bwack/C64C-250469-KiCAD-Replica/images/250469.gif

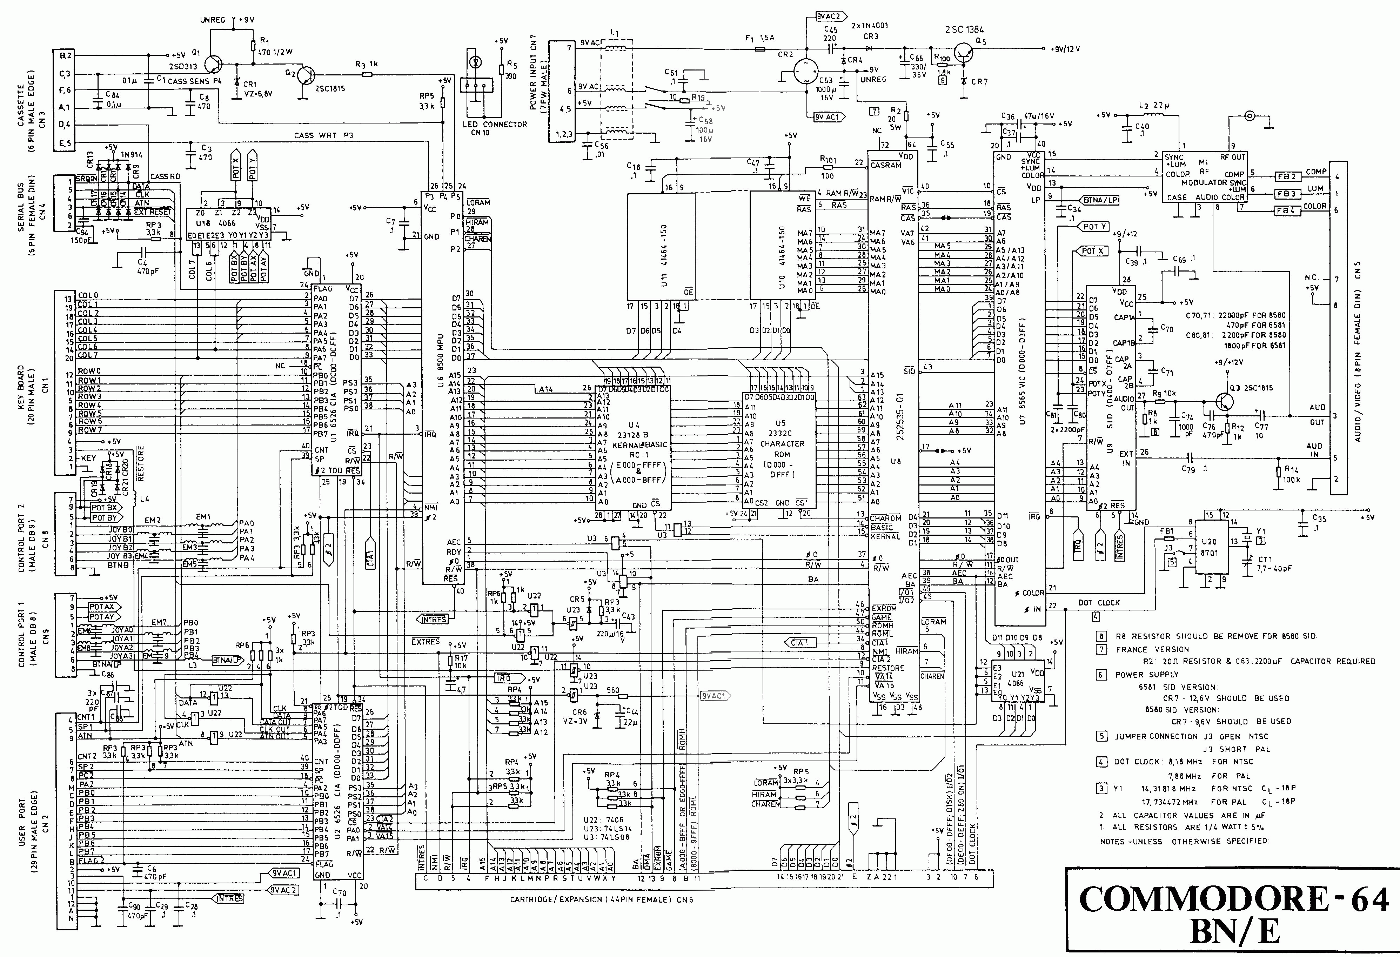
images/250469.gif
