bwack/C64C-250469-KiCAD-Replica/images/252312.jpg

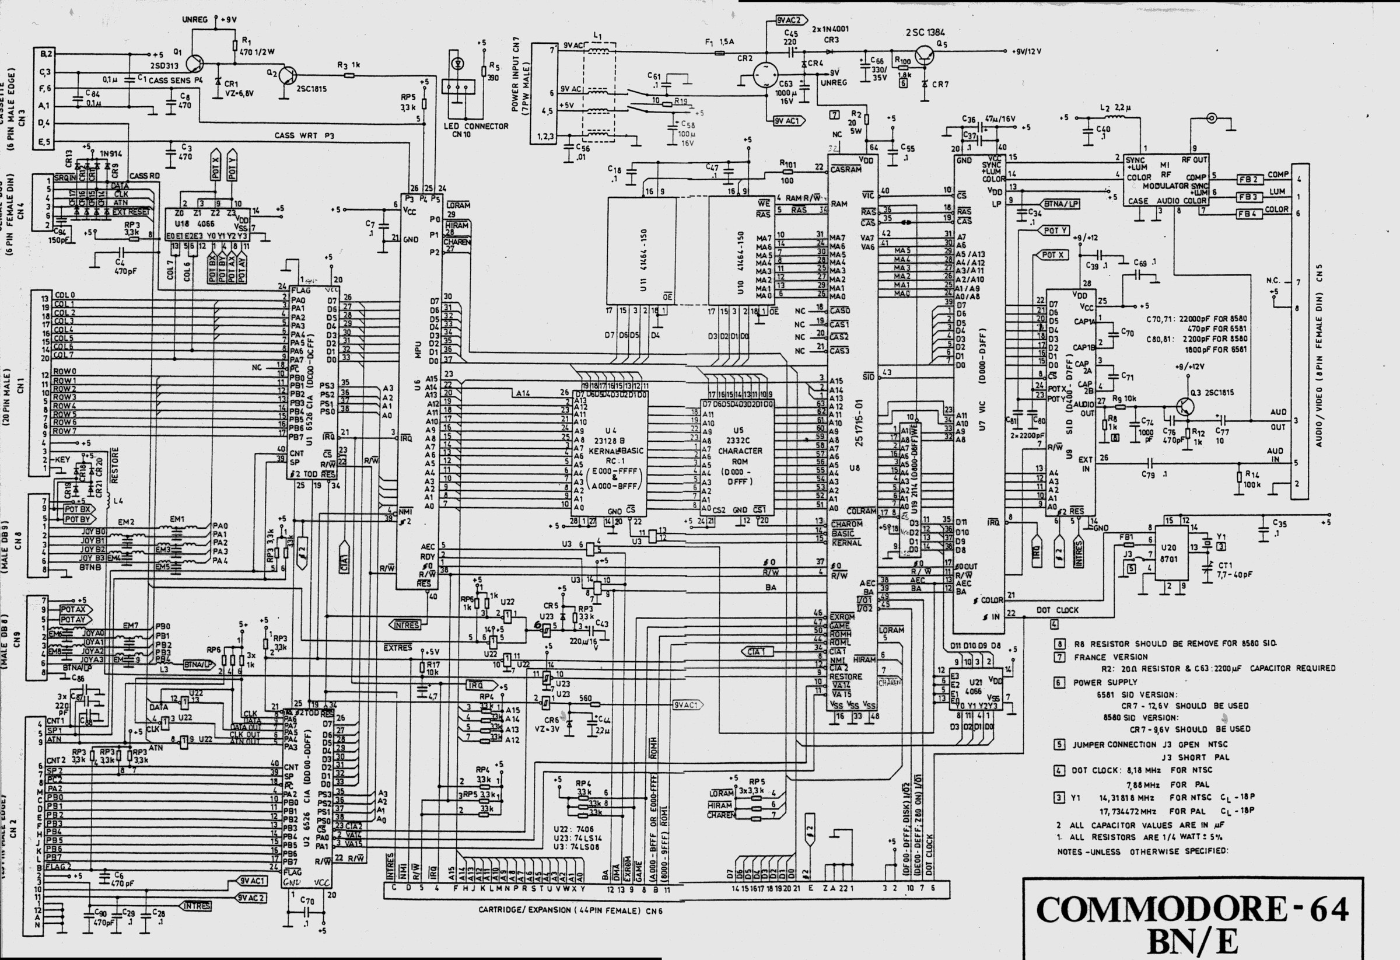
images/252312.jpg
