bwack/C64C-250469-KiCAD-Replica/C64-250469-KiCad.kicad_sch

## KiCad design C64-250469-KiCad.kicad_sch (2023-05-16)

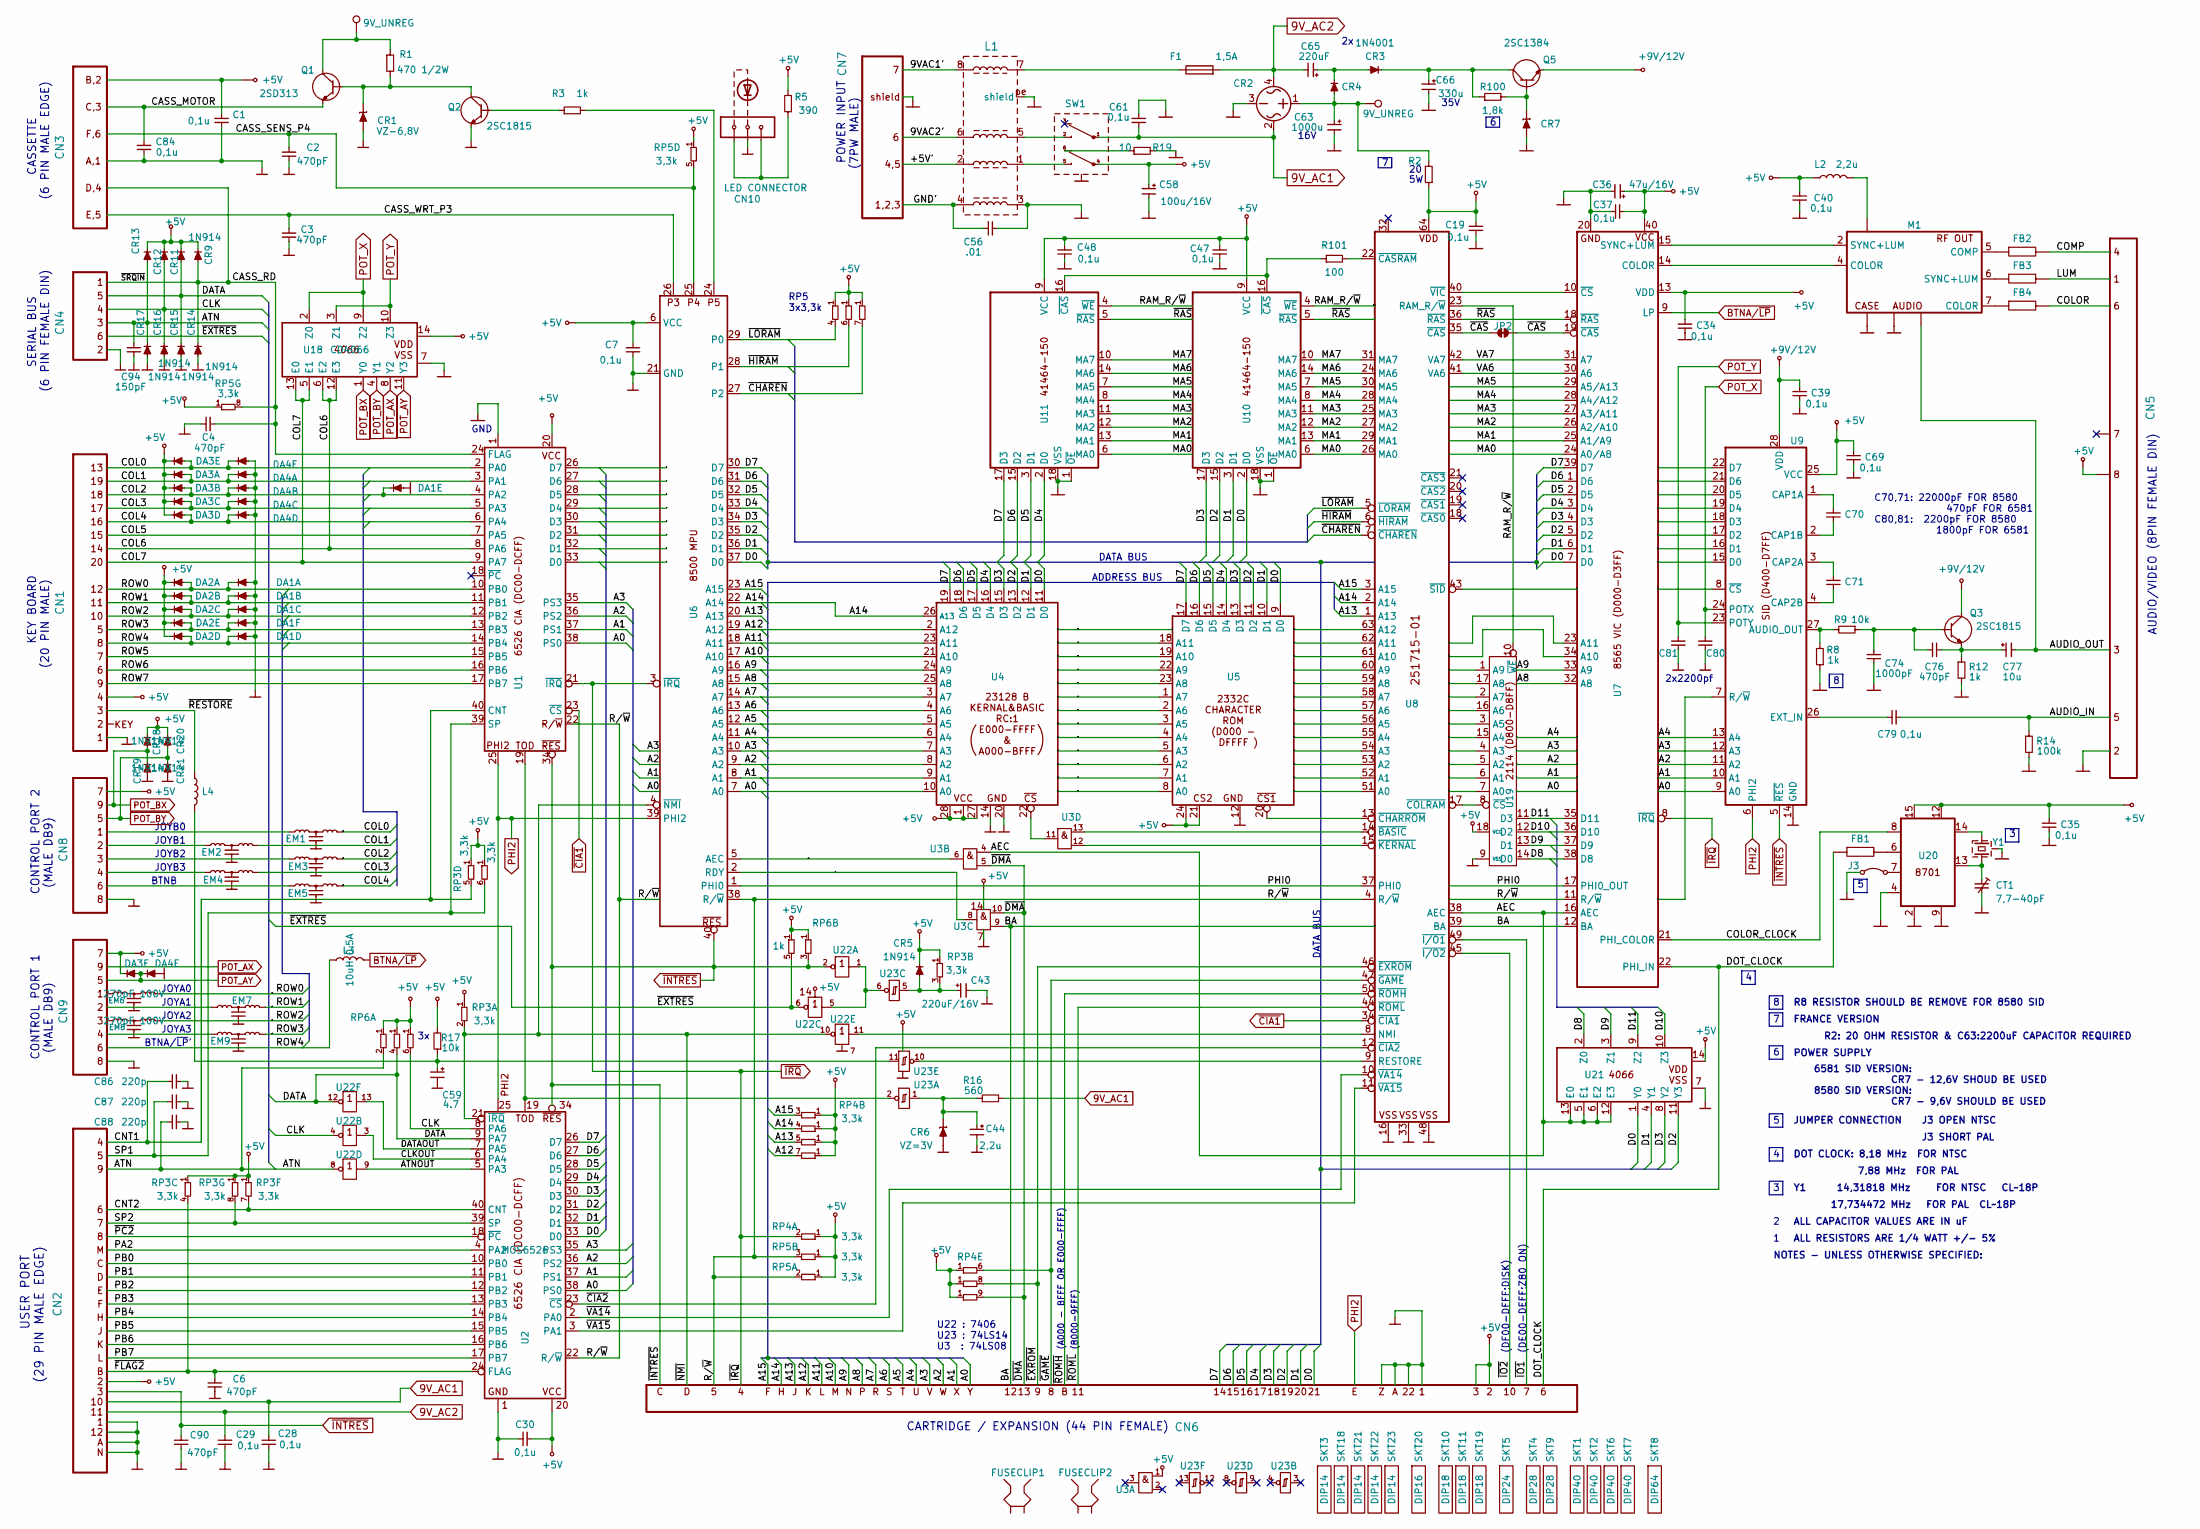
[picture p8: schematic C64-250469-KiCad.kicad_sch]

Parts:
C1, C7, C19, C28, C29, C30, C34, C35, C37, C39, C40, C47, C48, C61, C69, C79, C84: 0,1u; CAP_DISC_P100mil; Mouser 81-RCER71H104K0K1H3B
C2, C3, C4, C6, C76, C90: 470pF; CAP_DISC_P100mil; Mouser 81-RCER71H471K0M1H3A
C36: 47u/16V; CAP_RADIAL_P5.08MM_D6MM; Mouser 667-ECA-1CM470B
C43: 220uF/16V; CAP_RADIAL_P5.08MM_D6MM; Mouser 667-ECA-1CHG221B
C44: 2,2u; CAP_RADIAL_P5.08MM_D6MM; Mouser 667-ECA-1HHG2R2B
C56: .01; CAP_DISC_P100mil; Mouser 81-RCER71H103K0M1H3A
C58: 100u/16V; CAP_RADIAL_P5.12MM_D10MM; Mouser 667-ECA-1CHG101B
C59: 4.7; CAP_RADIAL_P5.08MM_D6MM; Mouser 667-ECE-A1EKS4R7B
C63: 1000u; CAP_AXIAL_BIG; Mouser 594-MAL212535102E3
C65: 220uF; CAP_RADIAL_P5.12MM_D12MM; Mouser 667-EEU-EB1E221SB
C66: 330u; CAP_RADIAL_P5.12MM_D12MM; Mouser 667-ECA-1VM471B
C70, C71: SeeTable; CAP_DISC_P100mil; Mouser 81-RCER71H223K0K1H3B
C74: 1000pF; CAP_DISC_P100mil; Mouser 81-RCER71H102K0M1H3A
C77: 10u; CAP_RADIAL_P5.08MM_D6MM; Mouser 667-ECA-1EM100B
C80, C81: 2200pF; CAP_DISC_P100mil; Mouser 81-RCER71H222K0M1H3A
C86, C87, C88: 220p; CAP_DISC_P100mil; Mouser 81-RCER71H221K0M1H3A
C94: 150pF; CAP_DISC_P100mil; Mouser 81-RCE5C1H151J0K1H3B
CN1: KEYBOARD_CONN_20pinlist; Mouser 855-M20-9992045
CN2: EDGE_CON_24P_USERPORT
CN3: EDGE_CON_12P_TAPE
CN4: SERIAL_CON_DIN6
CN5: AV_CON_DIN8
CN6: EXPANSION_PORT
CN7: POWER_CON_D7_250407
CN8, CN9: JOYPORT_DB9; Digi-Key 625-009-262-033-ND
CN10: LED CONNECTOR; LED; Mouser 855-M20-9992045
CR1: VZ-6,8V; RECTIFIER; Mouser 78-1N5235B
CR2: BRIDGE_RECTIFIER; Mouser 583-BR34
CR3, CR4: 1N4001; RECTIFIER; Mouser 625-1N4001-E3/54
CR5, CR9, CR11, CR12, CR13, CR14, CR15, CR16, CR17, CR18, CR19, CR20, CR21: 1N914; RECTIFIER; Mouser 78-1N4148
CR6: VZ=3V; RECTIFIER; Mouser 78-1N5225B-TAP
CR7: See [6] in schema; RECTIFIER; Mouser 78-1N5240B
CT1: 7,7-40pF; CAP_VARIABLE; Digi-Key 2447-GKG30015-ND
DA1, DA4: DIODE_ARRAY_COMMON_Anoda; diodepackage; Mouser NU
DA2, DA3: DIODE_ARRAY_COMMON_CATHODE; diodepackage; Mouser NU
EM1, EM2, EM3, EM4, EM5, EM6, EM7, EM8, EM9: 270pF 100V; T-FILTER; Mouser 81-DSS1NB32A271Q91A
F1: 1,5A; FUSE; Mouser 504-BK/AGC-1-1/2-R
FB1: FERRITE_BEAD_TWO_TURN; FERRITE_P200mil_STANDING; Mouser 81-BL02RN2R1M2B
FB2, FB3, FB4: FERRITE_BEAD; FERRITE_P200mil_STANDING; Mouser 81-BL01RN1A1F1J
FUSECLIP1, FUSECLIP2: Mouser 504-BK/1A1907-06-R
J3: JUMPER_NO
JP2: SolderJumper_Closed; JUMPER_CLOSED
L1: CHOKE; CHOKE_FILTER; Digi-Key ?
L2: 2,2u; INDUCTOR_P500mil; Mouser 652-78F2R2J-RC
L3, L4: 10uH 0.5A; INDUCTOR_P200mil; Mouser 80-SBT-0210
M1: Modulator
Q1: 2SD313; TO-220-3_Horizontal_TabDown_250407; Digi-Key TIP29AGOS-ND
Q2, Q3: 2SC1815; Q_NPN_ECB; Digi-Key 1514-2SC1815PBFREE-ND
Q5: 2SC1384; Q_NPN_ECB; Digi-Key KSD1616AGTATB-ND
R1: 470 1/2W; RESISTOR_AXIAL_600MIL; Digi-Key 13-MFR50SFRF52-470RCT-ND
R2: SeeTable; POWER_RESISTOR; Digi-Key Not Used
R3, R8, R12: 1k; RESISTOR_P200mil_STANDING; Digi-Key 13-MFR-25FTF52-1KCT-ND
R5: 390; RESISTOR_P200mil_STANDING; Digi-Key MFR-25FBF52-390R-ND
R9, R17: 10k; RESISTOR_P200mil_STANDING; Digi-Key 13-MFR-25FRF52-10KCT-ND
R14: 100k; RESISTOR_P200mil_STANDING; Digi-Key 13-MFR-25FRF52-100KCT-ND
R16: 560; RESISTOR_P200mil_STANDING; Digi-Key MFR-25FBF52-560R-ND
R19: 10; RESISTOR_AXIAL_600MIL; Digi-Key 13-MFR50SFTE52-10RCT-ND
R100: 1,8k; RESISTOR_P200mil_STANDING; Digi-Key 13-MFR-25FTE52-1K8CT-ND
R101: 100; RESISTOR_P200mil_STANDING; Digi-Key 100XBK-ND
RP3, RP5: 3,3k; RP_ARRAY_7WAY; Digi-Key 4608X-1-332LF-ND
RP4: 3,3k; RP_ARRAY_8WAY; Digi-Key 4609X-101-332LF-ND
RP6: 1k; RP_ARRAY_5WAY; Digi-Key 4606X-1-102LF-ND
SKT1, SKT2, SKT6, SKT7: DIP40; Digi-Key 1175-1481-ND
SKT3, SKT18, SKT21, SKT22, SKT23: DIP14; Digi-Key 1175-1476-ND
SKT4, SKT9: DIP28; Digi-Key 1175-1480-ND
SKT5: DIP24; Digi-Key 1175-2554-ND
SKT8: DIP64; Digi-Key D8864-42-ND
SKT10, SKT11, SKT19: DIP18; Digi-Key 1175-1478-ND
SKT20: DIP16; Digi-Key 1175-1477-ND
SW1: POWER_SWITCH; Digi-Key 360-4016-ND
U1, U2: MOS6526; PDIP-40
U3: 74LS08; PDIP-14; Mouser 595-SN74HCT08N
U4: 27128B; PDIP-28
U5: 2332C; PDIP-24
U6: 8500; PDIP-40
U7: VIC_II; PDIP-40
U8: 251715-01; PLA_252535-01
U9: SID; PDIP-28
U10, U11: 4164 DRAM; PDIP-18
U18, U21: CD4066; PDIP-14; Digi-Key 296-2061-5-ND
U19: COLOR_RAM_2114; PDIP-18
U20: MOS8701; PDIP-16
U22: 74LS06; PDIP-14; Mouser 595-SN7406NE4
U23: 74LS14; PDIP-14; Mouser 595-SN74HCT14N
Y1: 17.734475 MHz; CRYSTAL; Digi-Key 887-2042-ND

Connections:
9VAC1': CN7.7, L1.8
9VAC2': CN7.6, L1.6
9V_AC1: C28.1, C61.2, CN2.10, CR2.2, R16.2, SW1.1
9V_AC2: C29.1, C65.2, CN2.11, CR2.4, F1.2
9V_UNREG: C63.1, CR2.1, CR4.2 (A), Q1.C, R1.1, R2.2
+5V: C1.1, C7.1, C19.1, C30.2, C34.1, C35.1, C36.1, C37.2, C40.1, C47.1, C48.1, C58.1, C69.1, CN1.4, CN2.2, CN3.2, CN3.B, CN5.8 (VCC), CN6.2, CN6.3, CN8.7, CN9.7, CR5.1 (KATODE), CR9.1 (KATODE), CR11.1 (KATODE), CR12.1 (KATODE), CR13.1 (KATODE), CR18.1 (KATODE), CR20.1 (KATODE), DA2.4 (KATODE), DA3.4 (KATODE), L2.1, R2.1, R5.2, R17.2, RP3.1, RP4.1, RP5.1, RP6.1, SW1.4, U1.20 (VCC), U2.20 (VCC), U3.1, U3.14 (VDD), U4.1 (VCC), U4.27 (VCC), U4.28 (VCC), U5.21 (CS2), U5.24 (VCC), U6.6 (VCC), U7.13 (VDD), U7.40 (GND), U8.64 (VDD), U9.25 (VCC), U10.9 (VCC), U11.9 (VCC), U18.14 (VDD), U19.18 (VCC), U20.12, U20.15, U21.14 (VDD), U22.14, U23.14
+5V': CN7.4, CN7.5, L1.2
+9V/12V: C39.1, Q3.C, Q5.E, U9.28 (VDD)
A0: CN6.Y, U1.38 (PS0), U2.38 (PS0), U4.10 (A0), U5.8 (A0), U6.7 (A0), U8.51 (A0), U9.9 (A0), U19.7 (A0)
A1: CN6.X, U1.37 (PS1), U2.37 (PS1), U4.9 (A1), U5.7 (A1), U6.8 (A1), U8.52 (A1), U9.10 (A1), U19.6 (A1)
A2: CN6.W, U1.36 (PS2), U2.36 (PS2), U4.8 (A2), U5.6 (A2), U6.9 (A2), U8.53 (A2), U9.11 (A2), U19.5 (A2)
A3: CN6.V, U1.35 (PS3), U2.35 (PS3), U4.7 (A3), U5.5 (A3), U6.10 (A3), U8.54 (A3), U9.12 (A3), U19.4 (A3)
A4: CN6.U, U4.6 (A4), U5.4 (A4), U6.11 (A4), U8.55 (A4), U9.13 (A4), U19.15 (A4)
A5: CN6.T, U4.5 (A5), U5.3 (A5), U6.12 (A5), U8.56 (A5), U19.3 (A5)
A6: CN6.S, U4.4 (A6), U5.2 (A6), U6.13 (A6), U8.57 (A6), U19.16 (A6)
A7: CN6.R, U4.3 (A7), U5.1 (A7), U6.14 (A7), U8.58 (A7), U19.2 (A7)
A8: CN6.P, U4.25 (A8), U5.23 (A8), U6.15 (A8), U7.32 (A8), U8.59 (A8), U19.17 (A8)
A9: CN6.N, U4.24 (A9), U5.22 (A9), U6.16 (A9), U7.33 (A9), U8.60 (A9), U19.1 (A9)
A10: CN6.M, U4.21 (A10), U5.19 (A10), U6.17 (A10), U7.34 (A10), U8.61 (A10)
A11: CN6.L, U4.23 (A11), U5.18 (A11), U6.18 (A11), U7.23 (A11), U8.62 (A11)
A12: CN6.K, RP4.7, U4.2 (A12), U6.19 (A12), U8.63 (A12)
A13: CN6.J, RP4.5, U6.20 (A13), U8.1 (A13)
A14: CN6.H, RP4.4, U4.26 (A13), U6.22 (A14), U8.2 (A14)
A15: CN6.F, RP4.3, U6.23 (A15), U8.3 (A15)
AEC: U3.4, U7.16 (AEC), U8.38 (AEC), U21.5 (E1), U21.6 (E2), U21.12 (E3), U21.13 (E0)
AEC&~DMA: U3.6, U6.5 (AEC)
ATN: C88.2, C94.1, CN2.9, CN4.3, CR13.2 (A), CR17.1 (KATODE), RP6.2, U22.8
ATNOUT: U2.5 (PA3), U22.9
AUDIO_IN: C79.2, CN5.5 (AUDIO_IN), R14.1
AUDIO_OUT: C77.2, CN5.3 (AUDIO_OUT), M1.8 (AUDIO)
BA: CN6.12, U3.9, U7.12 (BA), U8.39 (BA)
BTNA/~LP: L3.2, U7.9 (LP)
CASS_MOTOR: C84.1, CN3.3, CN3.C, Q1.E
CASS_RD: C4.1, CN3.4, CN3.D, CN4.1, CR9.2 (A), CR14.1 (KATODE), RP5.8, U1.24 (FLAG)
CASS_SENS_P4: C2.1, CN3.6, CN3.F, RP5.5, U6.25 (P4)
CASS_WRT_P3: C3.1, CN3.5, CN3.E, U6.26 (P3)
CLK: CN4.4, CR12.2 (A), CR16.1 (KATODE), RP6.6, U2.8 (PA6), U22.4
CLKOUT: U2.6 (PA4), U22.3
CNT1: C86.2, CN2.4, RP3.5, U1.40 (CNT)
CNT2: CN2.6, RP3.7, U2.40 (CNT)
COL0: CN1.13, DA3.6 (A), DA4.7 (KATODE), EM1.3, U1.2 (PA0)
COL1: CN1.19, DA3.1 (A), DA4.1 (KATODE), EM2.3, U1.3 (PA1)
COL2: CN1.18, DA1.6 (KATODE), DA3.2 (A), DA4.2 (KATODE), EM3.3, U1.4 (PA2)
COL3: CN1.17, DA3.3 (A), DA4.3 (KATODE), EM4.3, U1.5 (PA3)
COL4: CN1.16, DA3.5 (A), DA4.5 (KATODE), EM5.3, U1.6 (PA4)
COL5: CN1.15, U1.7 (PA5)
COL6: CN1.14, U1.8 (PA6), U18.6 (E2), U18.12 (E3)
COL7: CN1.20, U1.9 (PA7), U18.5 (E1), U18.13 (E0)
COLOR: CN5.6 (COLOR), FB4.2
COLOR_CLOCK: U7.21 (PHI_COLOR), U20.8
COMP: CN5.4 (COMP), FB2.2
D0: CN6.21, U1.33 (D0), U2.33 (D0), U4.11 (D0), U5.9 (D0), U6.37 (D0), U7.7 (D0), U9.15 (D0), U10.2 (D0), U21.1 (Y0)
D1: CN6.20, U1.32 (D1), U2.32 (D1), U4.12 (D1), U5.10 (D1), U6.36 (D1), U7.6 (D1), U9.16 (D1), U10.3 (D1), U21.4 (Y1)
D2: CN6.19, U1.31 (D2), U2.31 (D2), U4.13 (D2), U5.11 (D2), U6.35 (D2), U7.5 (D2), U9.17 (D2), U10.15 (D2), U21.11 (Y3)
D3: CN6.18, U1.30 (D3), U2.30 (D3), U4.15 (D3), U5.13 (D3), U6.34 (D3), U7.4 (D3), U9.18 (D3), U10.17 (D3), U21.8 (Y2)
D4: CN6.17, U1.29 (D4), U2.29 (D4), U4.16 (D4), U5.14 (D4), U6.33 (D4), U7.3 (D4), U9.19 (D4), U11.2 (D0)
D5: CN6.16, U1.28 (D5), U2.28 (D5), U4.17 (D5), U5.15 (D5), U6.32 (D5), U7.2 (D5), U9.20 (D5), U11.3 (D1)
D6: CN6.15, U1.27 (D6), U2.27 (D6), U4.18 (D6), U5.16 (D6), U6.31 (D6), U7.1 (D6), U9.21 (D6), U11.15 (D2)
D7: CN6.14, U1.26 (D7), U2.26 (D7), U4.19 (D7), U5.17 (D7), U6.30 (D7), U7.39 (D7), U9.22 (D7), U11.17 (D3)
D8: U7.38 (D8), U19.14 (D0), U21.2 (Z0)
D9: U7.37 (D9), U19.13 (D1), U21.3 (Z1)
D10: U7.36 (D10), U19.12 (D2), U21.10 (Z3)
D11: U7.35 (D11), U19.11 (D3), U21.9 (Z2)
DATA: CN4.5, CR11.2 (A), CR15.1 (KATODE), RP6.4, U2.9 (PA7), U22.12
DATAOUT: U2.7 (PA5), U22.13
DOT_CLOCK: CN6.6, FB1.1, U7.22 (PHI_IN)
GND: C1.2, C2.2, C3.2, C4.2, C6.2, C7.2, C19.2, C28.2, C29.2, C30.1, C34.2, C35.2, C36.2, C37.1, C39.2, C40.2, C43.2, C44.2, C47.2, C48.2, C56.2, C58.2, C59.2, C61.1, C63.2, C66.2, C69.2, C74.2, C80.2, C81.2, C84.2, C86.1, C87.1, C88.1, C90.2, C94.2, CN1.1, CN2.1, CN2.12, CN2.A, CN2.N, CN3.1, CN3.A, CN4.2, CN5.2 (GND), CN6.1, CN6.22, CN6.A, CN6.Z, CN7.pe (shield), CN8.8, CN9.8, CN10.2, CR1.2 (A), CR2.3, CR6.2 (A), CR7.2 (A), CR14.2 (A), CR15.2 (A), CR16.2 (A), CR17.2 (A), CR19.2 (A), CR21.2 (A), CT1.2, DA1.4 (A), DA4.4 (A), EM1.2, EM2.2, EM3.2, EM4.2, EM5.2, EM6.2, EM7.2, EM8.2, EM9.2, J3.1, L1.3, L1.pe (shield), M1.3 (AGND), M1.CASE, Q2.E, R8.1, R12.2, R14.2, R19.2, SW1.pe (SHIELD), U1.1 (GND), U2.1 (GND), U3.7 (VSS), U4.14 (GND), U4.20 (GND), U5.12 (GND), U6.21 (GND), U7.20 (GND), U8.16 (VSS), U8.33 (VSS), U8.48 (VSS), U9.14 (GND), U10.1 (~OE), U10.18 (VSS), U11.1 (~OE), U11.18 (VSS), U18.7 (VSS), U19.9 (VSS), U20.2, U20.4, U20.9, U21.7 (VSS), U22.7, U23.7, Y1.3
GND': C56.1, CN7.1, CN7.2, CN7.3, L1.4
LUM: CN5.1 (LUM), FB3.2
MA0: U7.24 (A0/A8), U8.26 (MA0), U10.6 (MA0), U11.6 (MA0)
MA1: U7.25 (A1/A9), U8.29 (MA1), U10.13 (MA1), U11.13 (MA1)
MA2: U7.26 (A2/A10), U8.27 (MA2), U10.12 (MA2), U11.12 (MA2)
MA3: U7.27 (A3/A11), U8.25 (MA3), U10.11 (MA3), U11.11 (MA3)
MA4: U7.28 (A4/A12), U8.28 (MA4), U10.8 (MA4), U11.8 (MA4)
MA5: U7.29 (A5/A13), U8.30 (MA5), U10.7 (MA5), U11.7 (MA5)
MA6: U8.24 (MA6), U10.14 (MA6), U11.14 (MA6)
MA7: U8.31 (MA7), U10.10 (MA7), U11.10 (MA7)
unnamed: C43.1, CR5.2 (A), RP3.3, U23.5
unnamed: C44.1, CR6.1 (KATODE), R16.1, U23.1
unnamed: C59.1, L4.2, R17.1, U23.11
unnamed: C65.1, CR3.2 (A), CR4.1 (KATODE)
unnamed: C66.1, CR3.1 (KATODE), Q5.C, R100.1
unnamed: C70.1, U9.1 (CAP1A)
unnamed: C70.2, U9.2 (CAP1B)
unnamed: C71.1, U9.3 (CAP2A)
unnamed: C71.2, U9.4 (CAP2B)
unnamed: C74.1, C76.1, Q3.B, R9.1
unnamed: C76.2, C77.1, Q3.E, R12.1
unnamed: C79.1, U9.26 (EXT_IN)
unnamed: CN8.1, EM1.1
unnamed: CN8.2, EM2.1
unnamed: CN8.3, EM3.1
unnamed: CN8.4, EM4.1
unnamed: CN8.6, EM5.1
unnamed: CN9.1, EM6.1
unnamed: CN9.2, EM7.1
unnamed: CN9.3, EM8.1
unnamed: CN9.4, EM9.1
unnamed: CN10.1, CN10.3, R5.1
unnamed: CR1.1 (KATODE), Q1.B, Q2.C, R1.2
unnamed: CR7.1 (KATODE), Q5.B, R100.2
unnamed: CT1.1, U20.13, Y1.2
unnamed: F1.1, L1.7
unnamed: FB1.2, U20.6
unnamed: FB2.1, M1.5 (COMP)
unnamed: FB3.1, M1.6 (SYNC+LUM)
unnamed: FB4.1, M1.7 (COLOR)
unnamed: J3.2, U20.7
unnamed: L1.1, SW1.5
unnamed: L1.5, SW1.2
unnamed: L2.2, M1.1 (VCC)
unnamed: M1.2 (SYNC+LUM), U7.15 (SYNC+LUM)
unnamed: M1.4 (COLOR), U7.14 (COLOR)
unnamed: Q2.B, R3.1
unnamed: R3.2, U6.24 (P5)
unnamed: R8.2, R9.2, U9.27 (AUDIO_OUT)
unnamed: R19.1, SW1.6
unnamed: R101.1, U10.16 (~CAS), U11.16 (~CAS)
unnamed: R101.2, U8.22 (~CASRAM)
unnamed: U1.19 (TOD), U2.19 (TOD), U23.2
unnamed: U3.11, U4.22 (~CS)
unnamed: U3.12, U8.15 (~KERNAL)
unnamed: U3.13, U8.14 (~BASIC)
unnamed: U5.20 (~CS1), U8.13 (~CHARROM)
unnamed: U7.10 (~CS), U8.40 (~VIC)
unnamed: U8.17 (~COLRAM), U19.8 (~CS)
unnamed: U20.14, Y1.1
unnamed: U22.1, U22.5, U23.6
unnamed: U8.8 (NMI), U22.11
unnamed: U8.9 (RESTORE), U23.10
PA2: CN2.M, U2.4 (PA2)
PB0: CN2.C, U2.10 (PB0)
PB1: CN2.D, U2.11 (PB1)
PB2: CN2.E, U2.12 (PB2)
PB3: CN2.F, U2.13 (PB3)
PB4: CN2.H, U2.14 (PB4)
PB5: CN2.J, U2.15 (PB5)
PB6: CN2.K, U2.16 (PB6)
PB7: CN2.L, U2.17 (PB7)
PHI0: U6.1 (PHI0), U7.17 (PHI0_OUT), U8.37 (PHI0)
PHI2: CN6.E, U1.25 (PHI2), U2.25 (PHI2), U6.39 (PHI2), U9.6 (PHI2)
POT_AX: CN9.9, U18.8 (Y2)
POT_AY: CN9.5, DA3.7 (A), DA4.6 (KATODE), U18.11 (Y3)
POT_BX: CN8.9, CR18.2 (A), CR19.1 (KATODE), U18.1 (Y0)
POT_BY: CN8.5, CR20.2 (A), CR21.1 (KATODE), U18.4 (Y1)
POT_X: C80.1, U9.24 (POTX), U18.2 (Z0), U18.9 (Z2)
POT_Y: C81.1, U9.23 (POTY), U18.3 (Z1), U18.10 (Z3)
RAM_R/~W: U8.23 (RAM_R/~W), U10.4 (~WE), U11.4 (~WE), U19.10 (~WE)
RDY: U3.8, U6.2 (RDY)
ROW0: CN1.12, DA1.1 (KATODE), DA2.1 (A), EM6.3, U1.10 (PB0)
ROW1: CN1.11, DA1.2 (KATODE), DA2.2 (A), EM7.3, U1.11 (PB1)
ROW2: CN1.10, DA1.3 (KATODE), DA2.3 (A), EM8.3, U1.12 (PB2)
ROW3: CN1.5, DA1.7 (KATODE), DA2.6 (A), EM9.3, U1.13 (PB3)
ROW4: CN1.8, CN9.6, DA1.5 (KATODE), DA2.5 (A), L3.1, U1.14 (PB4)
ROW5: CN1.7, U1.15 (PB5)
ROW6: CN1.6, U1.16 (PB6)
ROW7: CN1.9, U1.17 (PB7)
R/~W: CN6.5, RP5.2, RP5.3, U1.22 (R/~W), U2.22 (R/~W), U6.38 (R/~W), U7.11 (R/~W), U8.4 (R/~W), U9.7 (R/~W)
SP1: C87.2, CN2.5, RP3.6, U1.39 (SP)
SP2: CN2.7, RP3.8, U2.39 (SP)
VA6: U7.30 (A6), U8.41 (VA6)
VA7: U7.31 (A7), U8.42 (VA7)
~CAS: JP2.1, U7.19 (~CAS), U8.35 (~CAS)
~CHAREN: RP5.7, U6.27 (P2), U8.7 (~CHAREN)
~CIA1: U1.23 (~CS), U8.34 (~CIA1)
~CIA2: U2.23 (~CS), U8.12 (~CIA2)
~DMA: CN6.13, RP4.9, U3.5, U3.10
~EXROM: CN6.9, RP4.8, U8.46 (~EXROM)
~EXTRES: CN4.6, RP6.5, U22.6
~FLAG2: C6.1, CN2.B, RP3.4, U2.24 (FLAG)
~GAME: CN6.8, RP4.6, U8.47 (~GAME)
~HIRAM: RP5.6, U6.28 (P1), U8.6 (~HIRAM)
~INTRES: C90.1, CN2.3, CN6.C, RP6.3, U1.34 (~RES), U2.34 (~RES), U6.40 (~RES), U9.5 (~RES), U22.2
~IO1: CN6.7, U8.49 (~I/O1)
~IO2: CN6.10, U8.45 (~I/O2)
~IRQ: CN6.4, RP4.2, U1.21 (~IRQ), U6.3 (~IRQ), U7.8 (~IRQ)
~LORAM: RP5.4, U6.29 (P0), U8.5 (~LORAM)
~NMI: CN6.D, RP3.2, U2.21 (~IRQ), U6.4 (~NMI), U22.10
~PC2: CN2.8, U2.18 (~PC)
~RAS: U7.18 (~RAS), U8.36 (~RAS), U10.5 (~RAS), U11.5 (~RAS)
~RESTORE: CN1.3, L4.1
~ROMH: CN6.B, U8.50 (~ROMH)
~ROML: CN6.11, U8.44 (~ROML)
~SID: U8.43 (~SID), U9.8 (~CS)
~VA14: U2.2 (PA0), U8.10 (~VA14)
~VA15: U2.3 (PA1), U8.11 (~VA15)

Notes on the sheet:
JOYB3
(8000-9FFF)
J3 OPEN NTSC
DATA BUS
CARTRIDGE / EXPANSION (44 PIN FEMALE)
JUMPER CONNECTION
DOT CLOCK: 8,18 MHz FOR NTSC
FRANCE VERSION
16V
USER PORT (29 PIN MALE EDGE)
J3 SHORT PAL
2x2200pf
Y1 14,31818 MHz FOR NTSC CL~18P
JOYB2
GND
35V
RP5 3x3,3k
SERIAL BUS (6 PIN FEMALE DIN)
CONTROL PORT 2 (MALE DB9)
R8 RESISTOR SHOULD BE REMOVE FOR 8580 SID
(A000 - BFFF OR E000-FFFF)
JOYA0
BTNA/~{LP}'
JOYA2
POWER SUPPLY
(DF00-DFFF;DISK)
JOYA3
KEY BOARD (20 PIN MALE)
POWER INPUT (7PW MALE)
JOYA1
7,88 MHz FOR PAL
ALL CAPACITOR VALUES ARE IN uF
CASSETTE (6 PIN MALE EDGE)
6581 SID VERSION: CR7 - 12,6V SHOUD BE USED 8580 SID VERSION: CR7 - 9,6V SHOULD BE USED
NOTES - UNLESS OTHERWISE SPECIFIED:
ALL RESISTORS ARE 1/4 WATT +/- 5%
AUDIO/VIDEO (8PIN FEMALE DIN)
(DE00-DEFF;Z80 ON)
R2: 20 OHM RESISTOR & C63:2200uF CAPACITOR REQUIRED
JOYB1
U22 : 7406 U23 : 74LS14 U3 : 74LS08
C70,71: 22000pF FOR 8580 470pF FOR 6581 C80,81: 2200pF FOR 8580 1800pF FOR 6581
JOYB0
ADDRESS BUS
17,734472 MHz FOR PAL CL~18P
BTNB
CONTROL PORT 1 (MALE DB9)
